iliasam/OpenSimpleLidar/Mechanics/Base_plate/base_plate.png

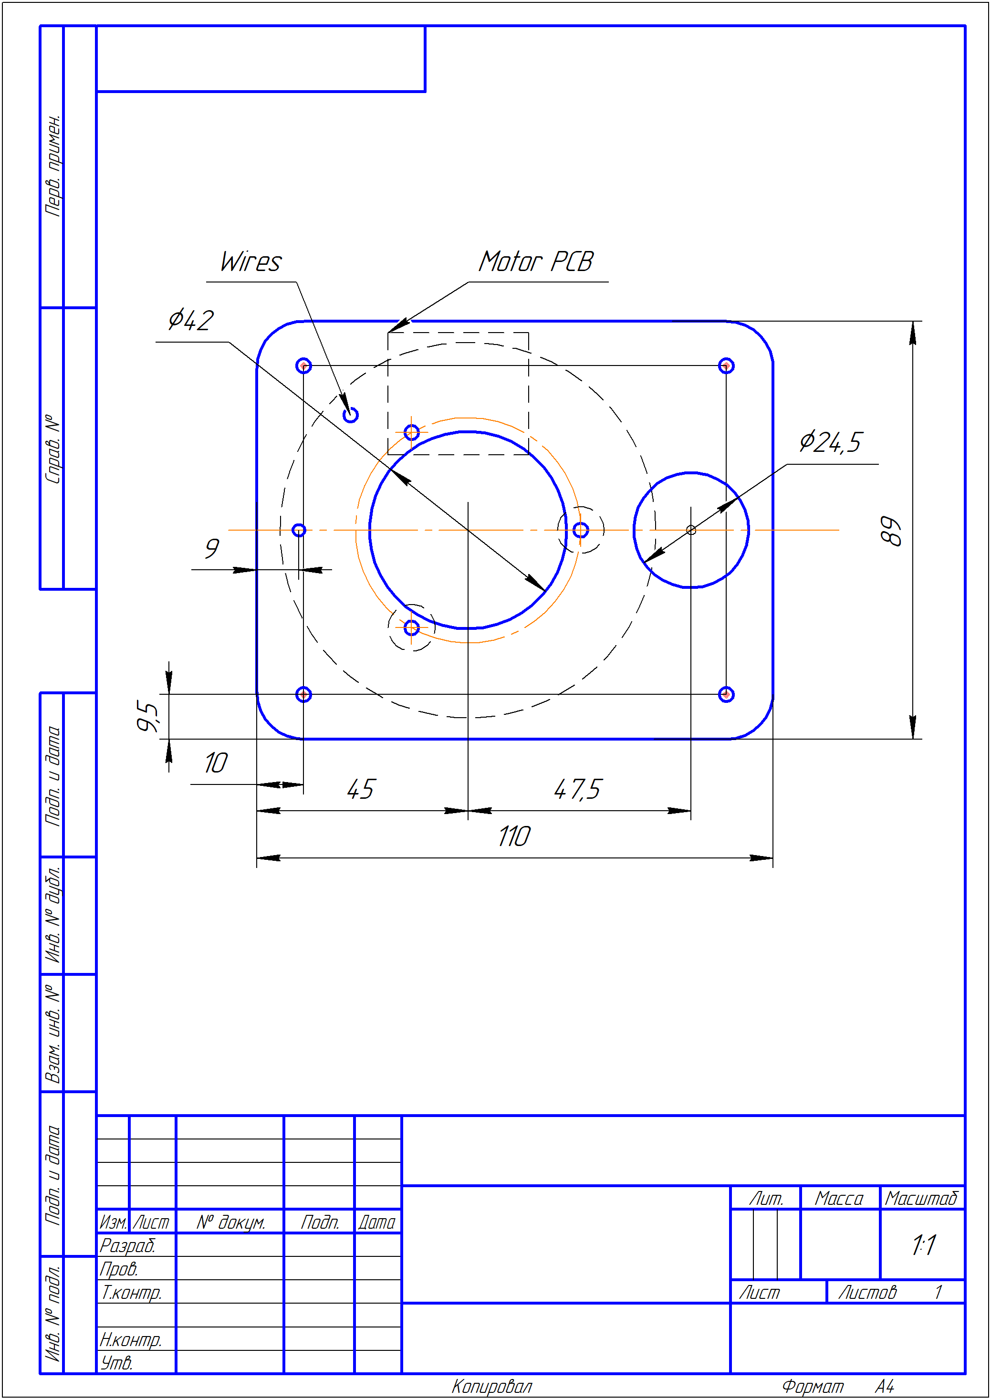
Mechanics/Base_plate/base_plate.png
