iliasam/OpenSimpleLidar/Mechanics/laser_angle.png

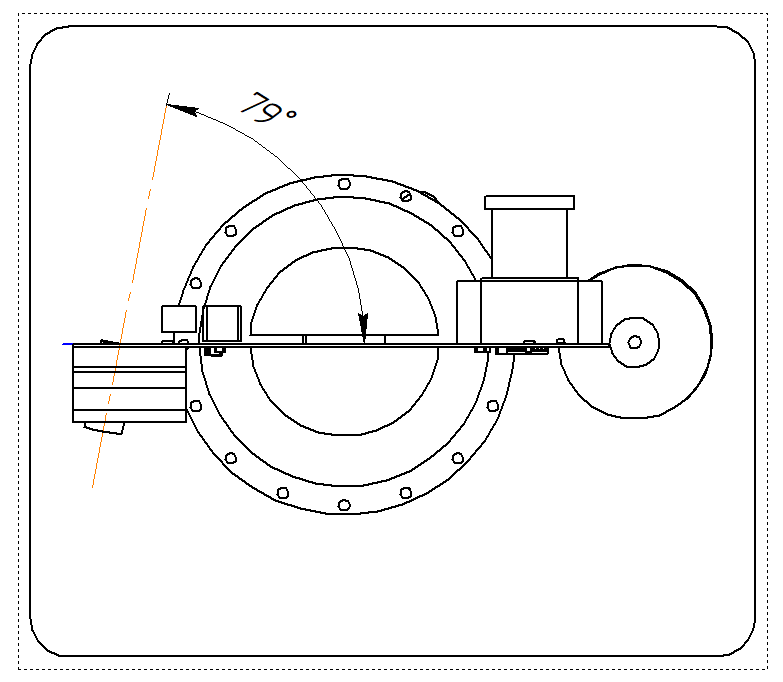
Mechanics/laser_angle.png
