iliasam/OpenSimpleLidar/Misc/filter_photo.jpg

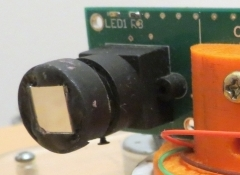
Misc/filter_photo.jpg
