iliasam/OpenSimpleLidar/Misc/finding_sensor_active_zone.png

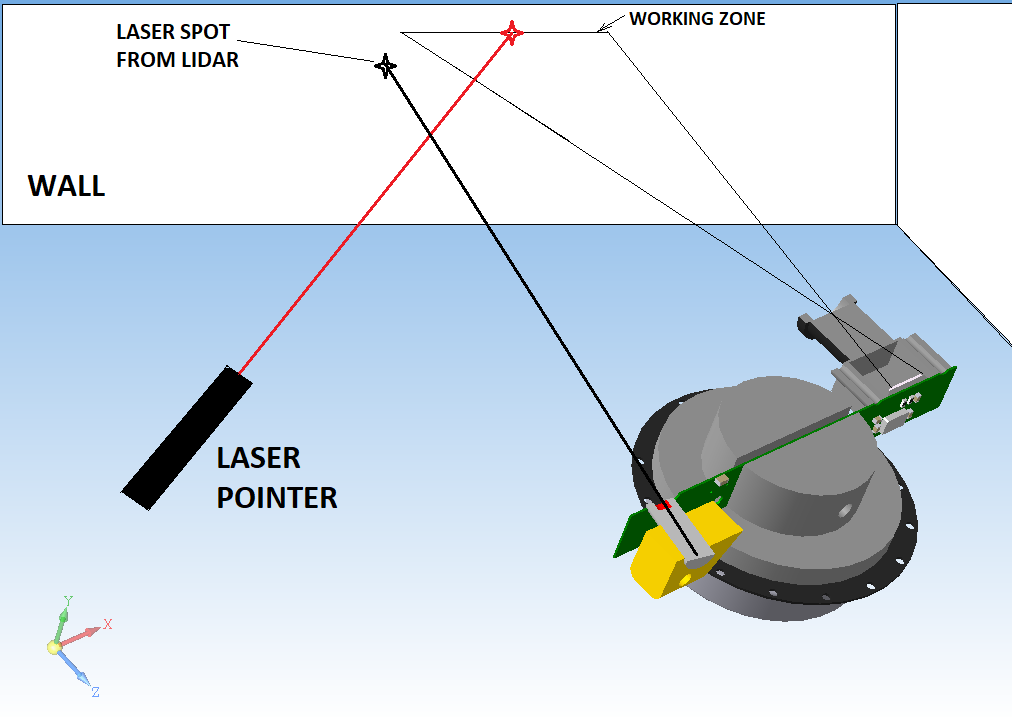
Misc/finding_sensor_active_zone.png
