iliasam/OpenSimpleLidar/Misc/interference_filter.png

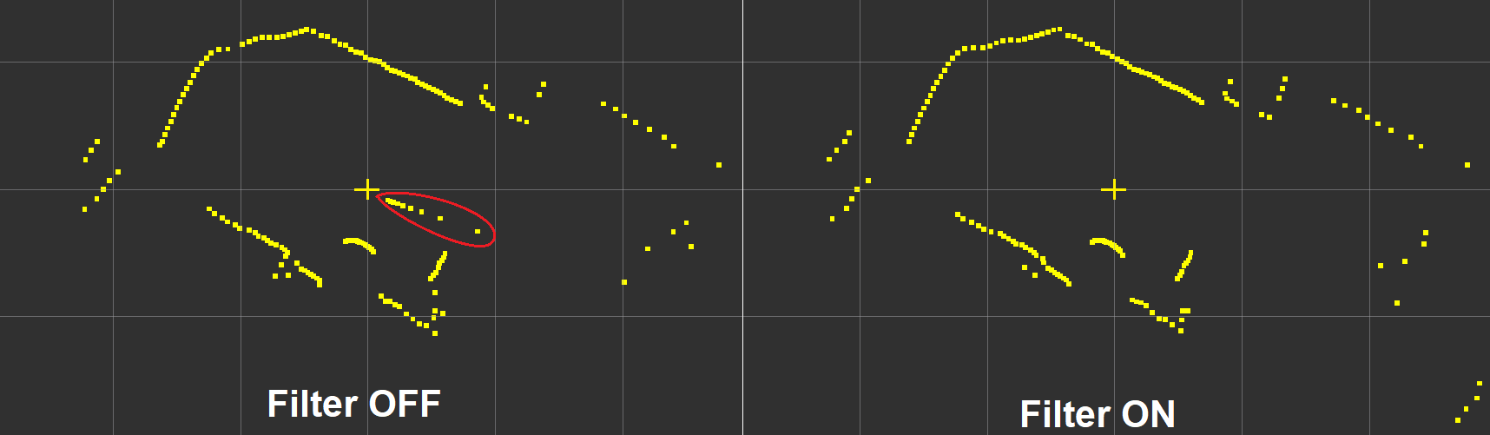
Misc/interference_filter.png
