iliasam/OpenSimpleLidar/Misc/Laser_alignment.png

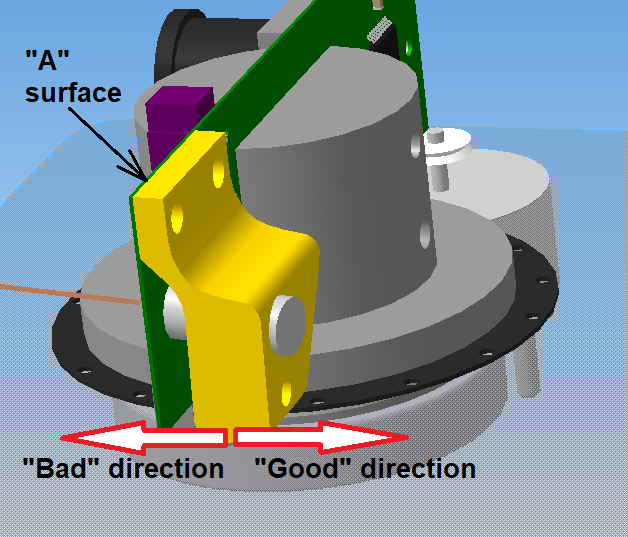
Misc/Laser_alignment.png
