iliasam/OpenSimpleLidar/Misc/Pictures/laser.jpg

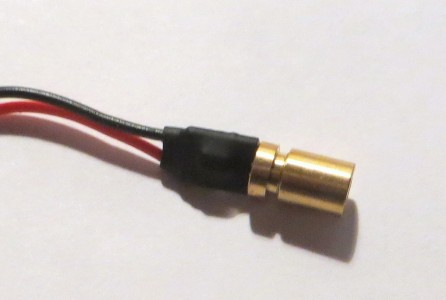
Misc/Pictures/laser.jpg
