iliasam/OpenSimpleLidar/Misc/Pictures/laser_holder.jpg

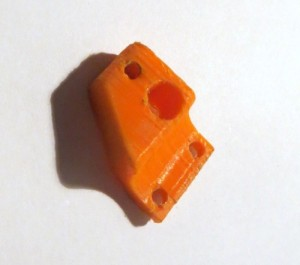
Misc/Pictures/laser_holder.jpg
