iliasam/OpenSimpleLidar/Misc/Pictures/pcb_holder1.jpg

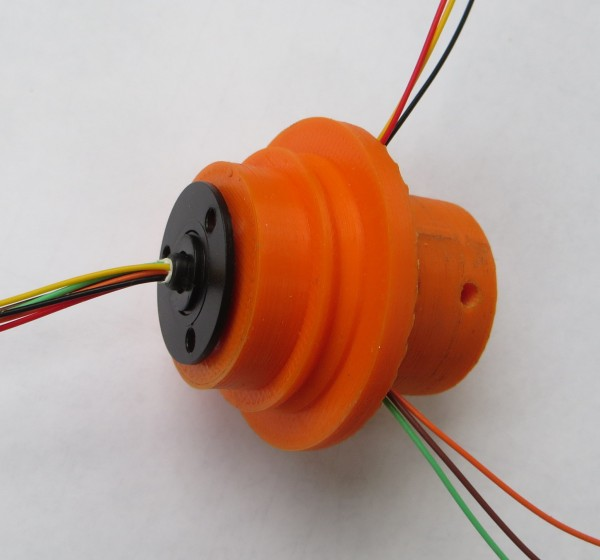
Misc/Pictures/pcb_holder1.jpg
