iliasam/OpenSimpleLidar/Misc/Pictures/pcb_holder2.JPG

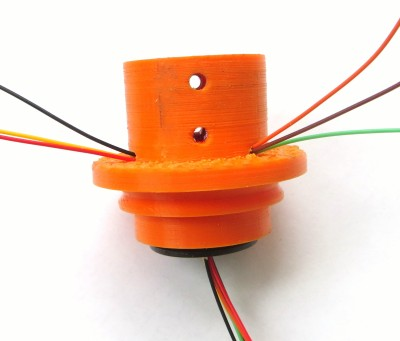
Misc/Pictures/pcb_holder2.JPG
