iliasam/OpenSimpleLidar/Misc/Pictures/pcb_holder_and_encoder.jpg

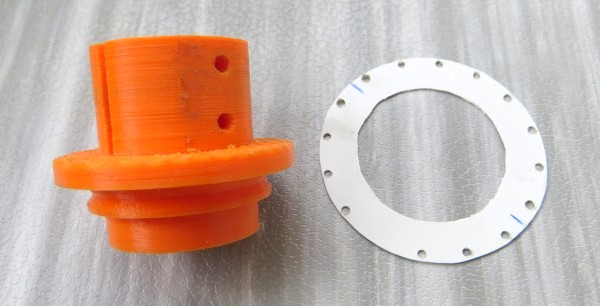
Misc/Pictures/pcb_holder_and_encoder.jpg
