iliasam/OpenSimpleLidar/Misc/Pictures/pic1.png

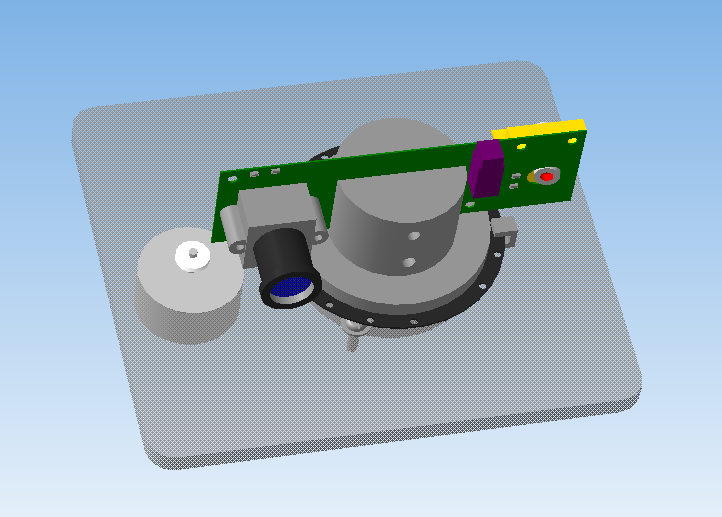
Misc/Pictures/pic1.png
