iliasam/OpenSimpleLidar/Misc/Pictures/pic2.png

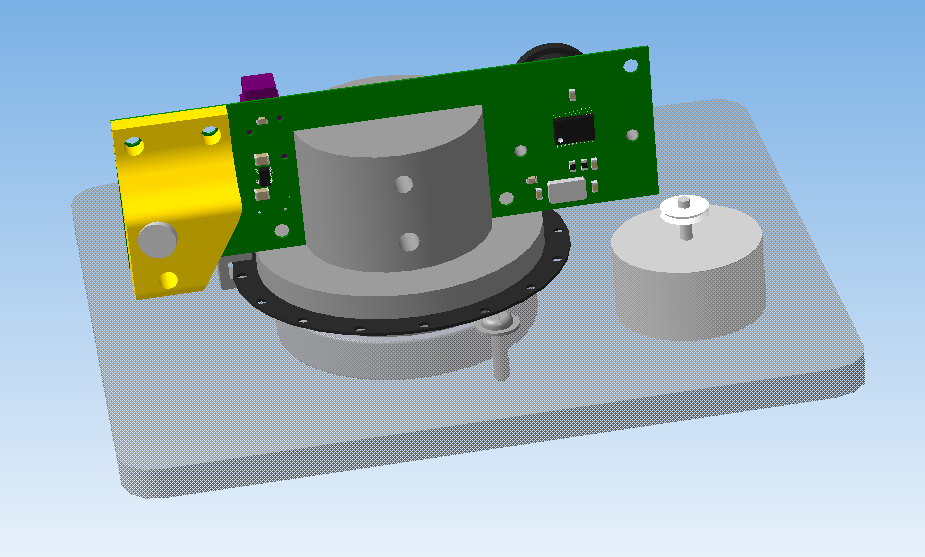
Misc/Pictures/pic2.png
