iliasam/OpenSimpleLidar/Misc/Pictures/pic3.png

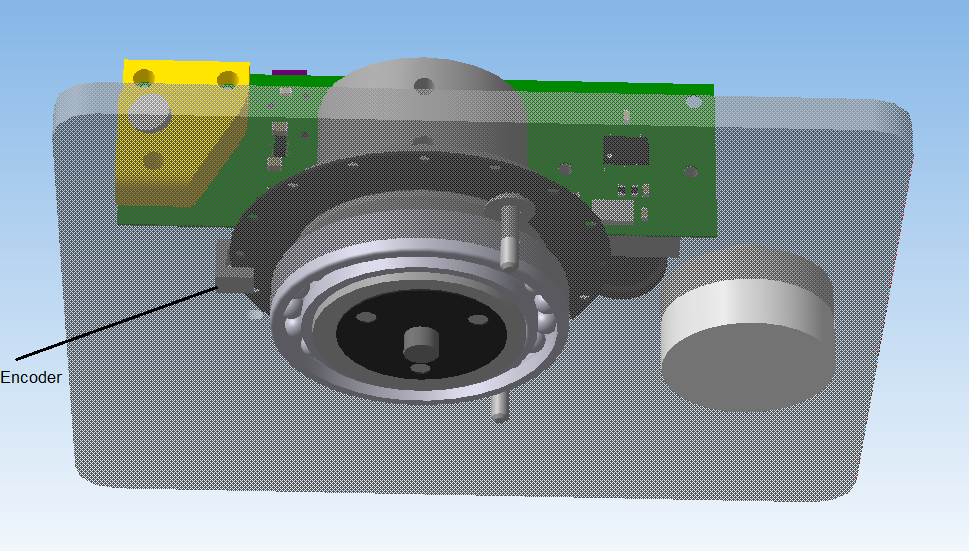
Misc/Pictures/pic3.png
