iliasam/OpenSimpleLidar/Misc/RobotStructure.png

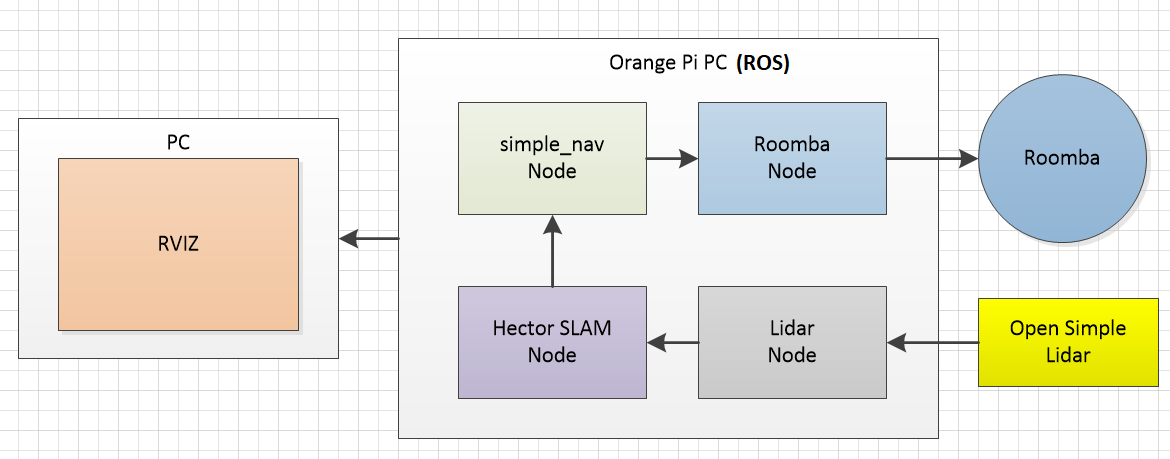
Misc/RobotStructure.png
