iliasam/OpenSimpleLidar/PCB/CommonPCB_v1.2M/PCB_top_v1.2M.png

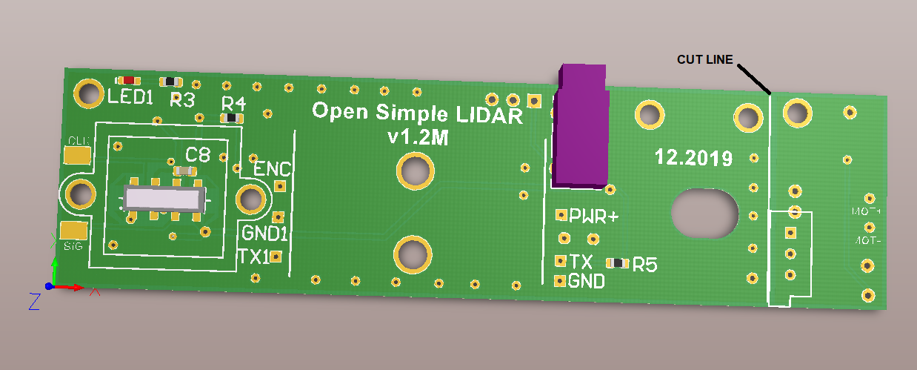
PCB/CommonPCB_v1.2M/PCB_top_v1.2M.png
