iliasam/OpenSimpleLidar/PCB/CommonPCB_v1.2M/Schematic_main_v1_2.png

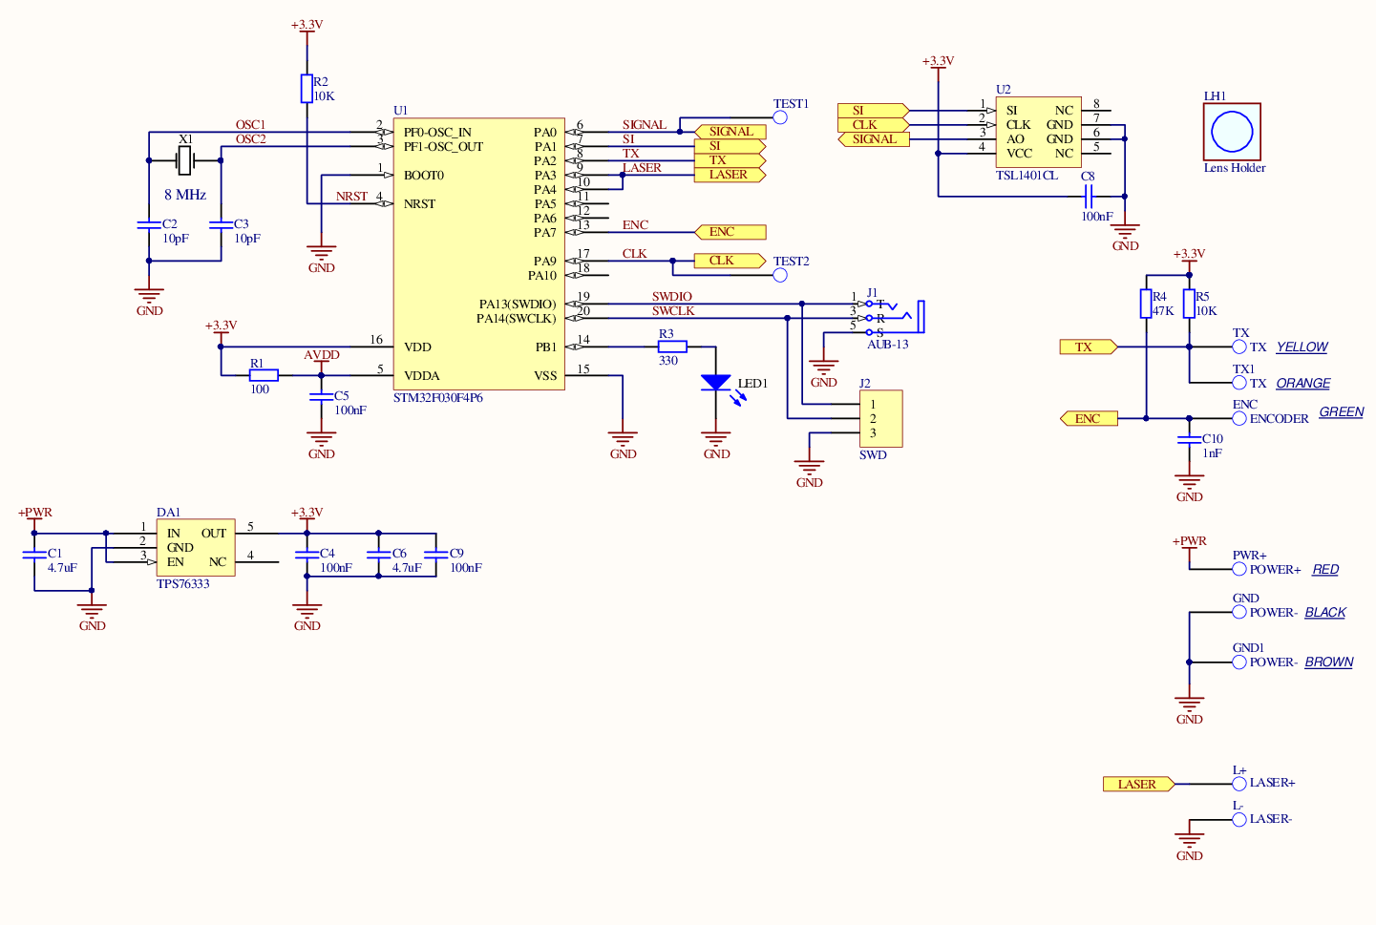
PCB/CommonPCB_v1.2M/Schematic_main_v1_2.png
