iliasam/OpenSimpleLidar/PCB/CommonPCB_v1.2M/Schematic_motor_v1.2.png

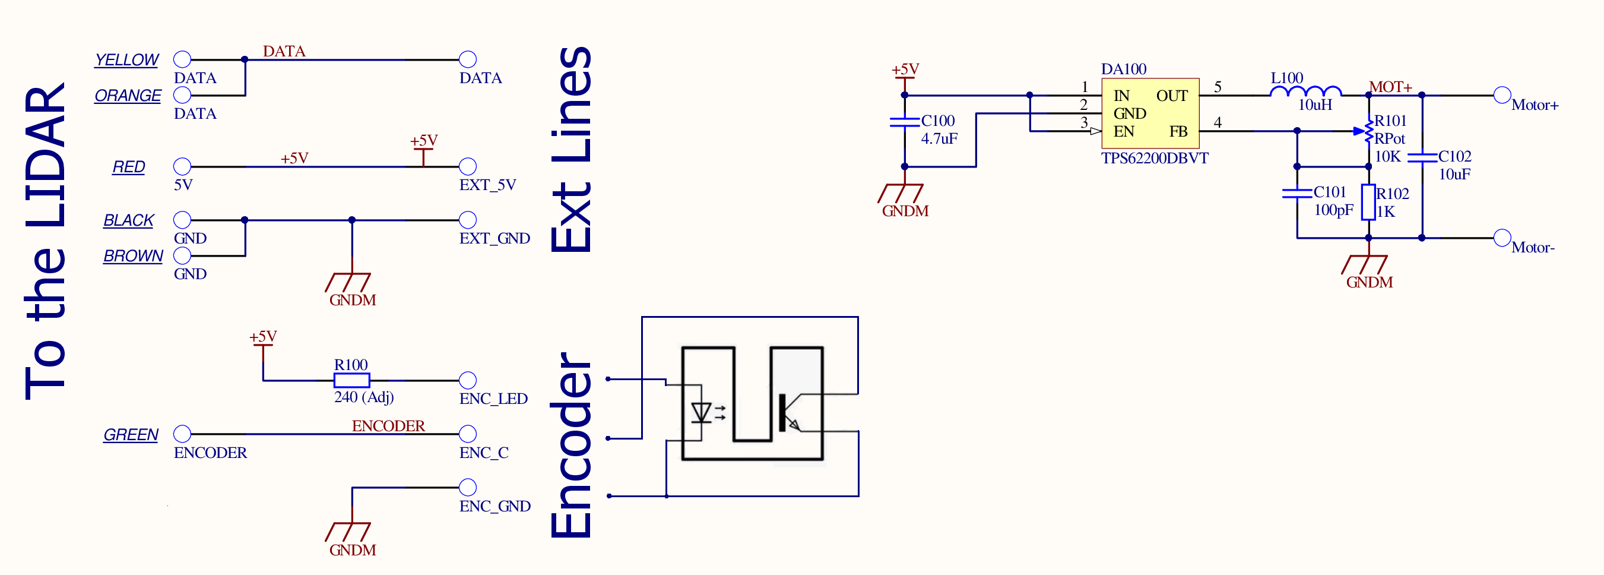
PCB/CommonPCB_v1.2M/Schematic_motor_v1.2.png
