iliasam/OpenSimpleLidar/PCB/SplittedPCB_v1.0_and_v1.1/MainPCB/PCB_assemply_top_v1.1.png

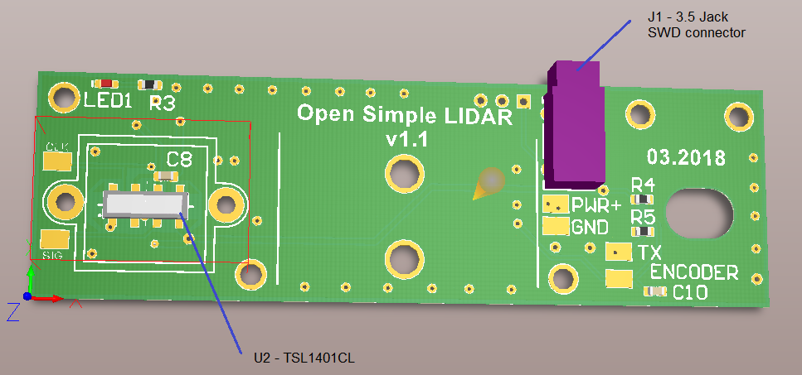
PCB/SplittedPCB_v1.0_and_v1.1/MainPCB/PCB_assemply_top_v1.1.png
