iliasam/OpenSimpleLidar/PCB/SplittedPCB_v1.0_and_v1.1/MotorPCB_v1.0/PCB_Connections.png

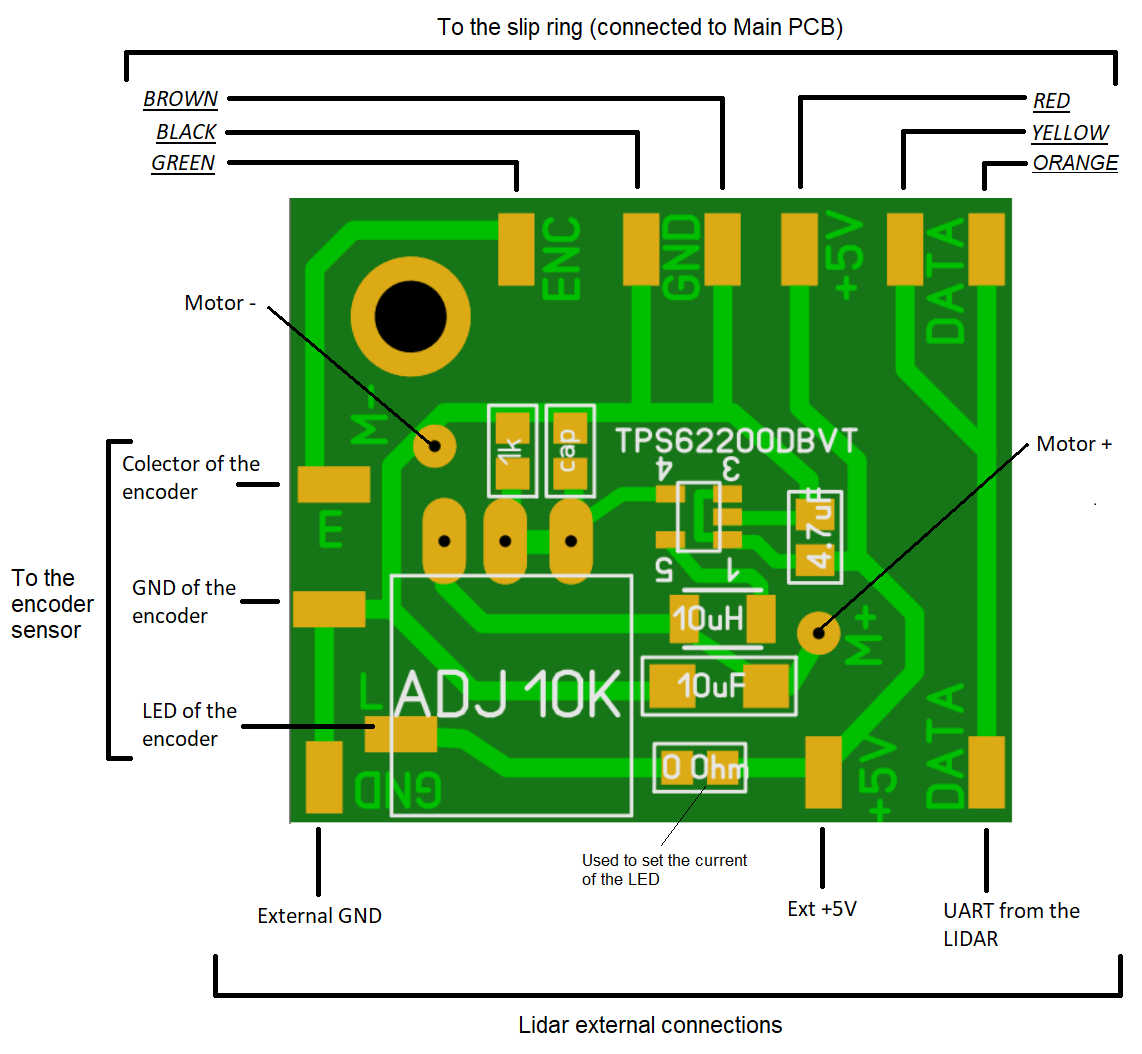
PCB/SplittedPCB_v1.0_and_v1.1/MotorPCB_v1.0/PCB_Connections.png
