iliasam/OpenSimpleLidar/Misc/Pictures/installing_sensor.jpg

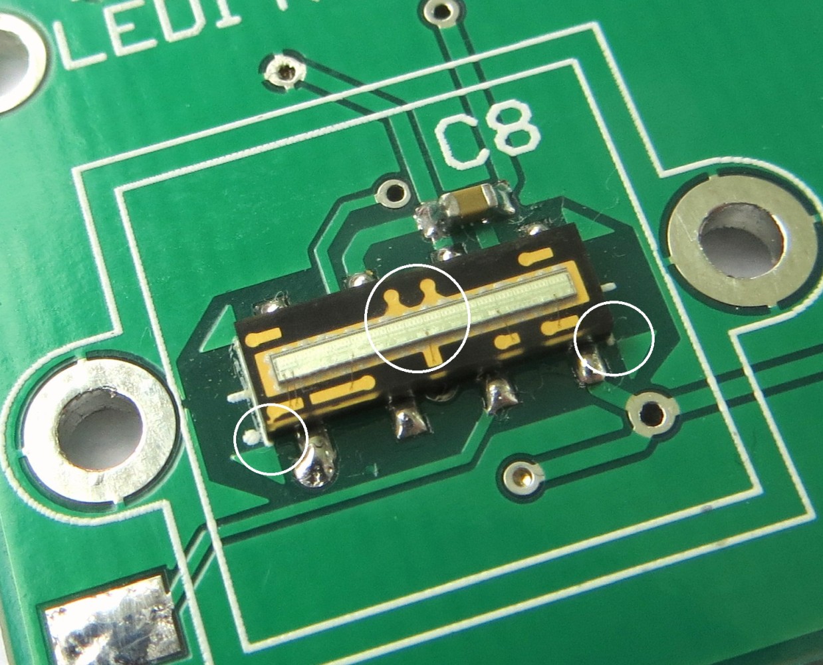
Misc/Pictures/installing_sensor.jpg
