iliasam/OpenSimpleLidar/Misc/Pictures/installing_slip_ring.jpg

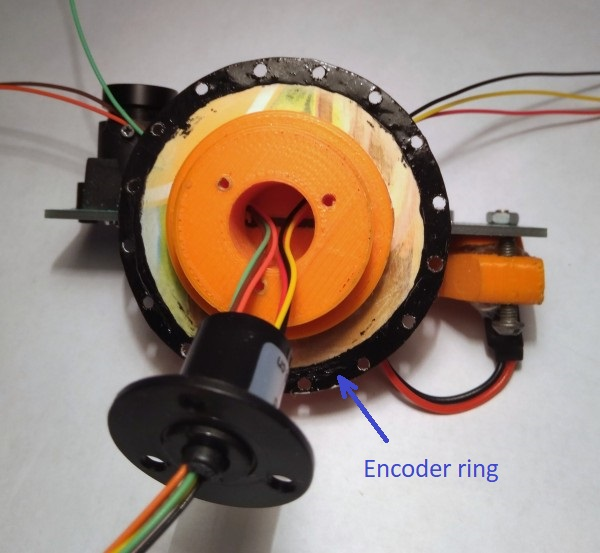
Misc/Pictures/installing_slip_ring.jpg
