iliasam/OpenSimpleLidar/Misc/Pictures/laser_holder_installed.jpg

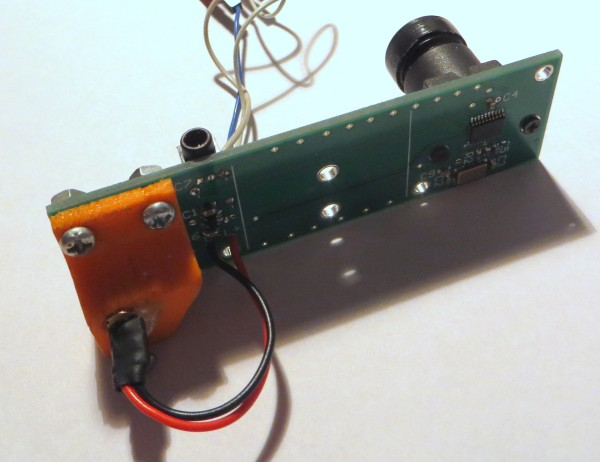
Misc/Pictures/laser_holder_installed.jpg
