iliasam/OpenSimpleLidar/Misc/Pictures/laser_installed.jpg

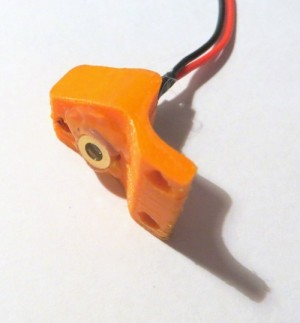
Misc/Pictures/laser_installed.jpg
