iliasam/OpenSimpleLidar/Misc/Pictures/lens_installed.jpg

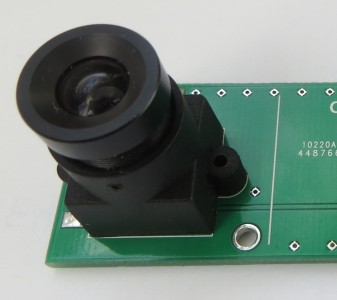
Misc/Pictures/lens_installed.jpg
