iliasam/OpenSimpleLidar/PCB/CommonPCB_v1.1M/PCB_assembly_bottom_v1.1M.png

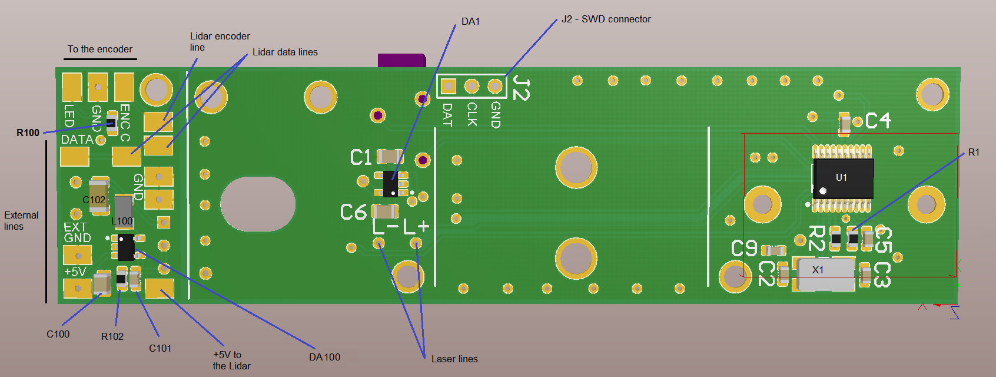
PCB/CommonPCB_v1.1M/PCB_assembly_bottom_v1.1M.png
