iliasam/OpenSimpleLidar/PCB/CommonPCB_v1.1M/PCB_assembly_top_v1.1M.png

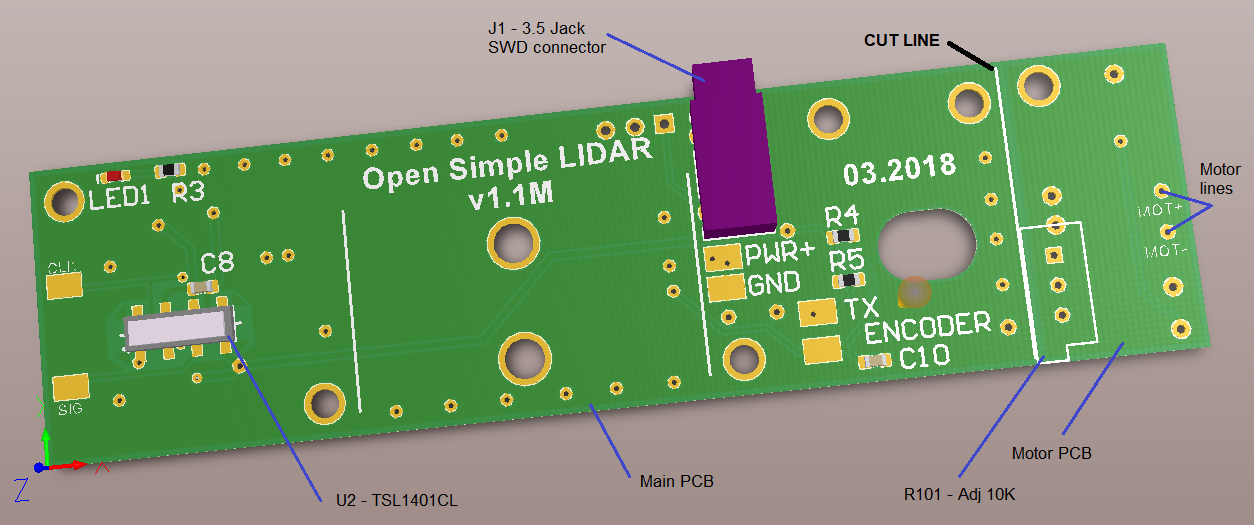
PCB/CommonPCB_v1.1M/PCB_assembly_top_v1.1M.png
