iliasam/OpenSimpleLidar/PCB/CommonPCB_v1.2/PCB_assembly_top_v1.2.png

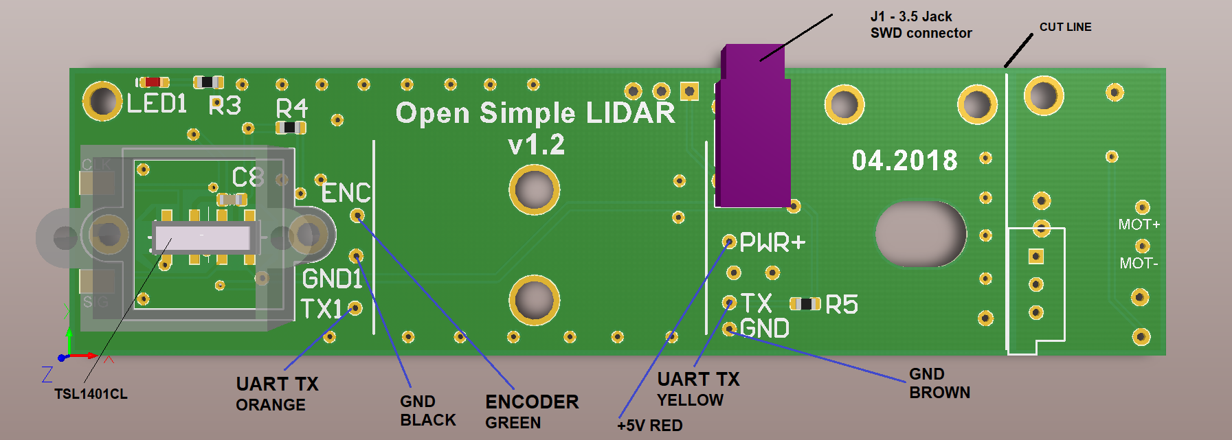
PCB/CommonPCB_v1.2/PCB_assembly_top_v1.2.png
