iliasam/OpenSimpleLidar/Misc/test_laser_on.jpg

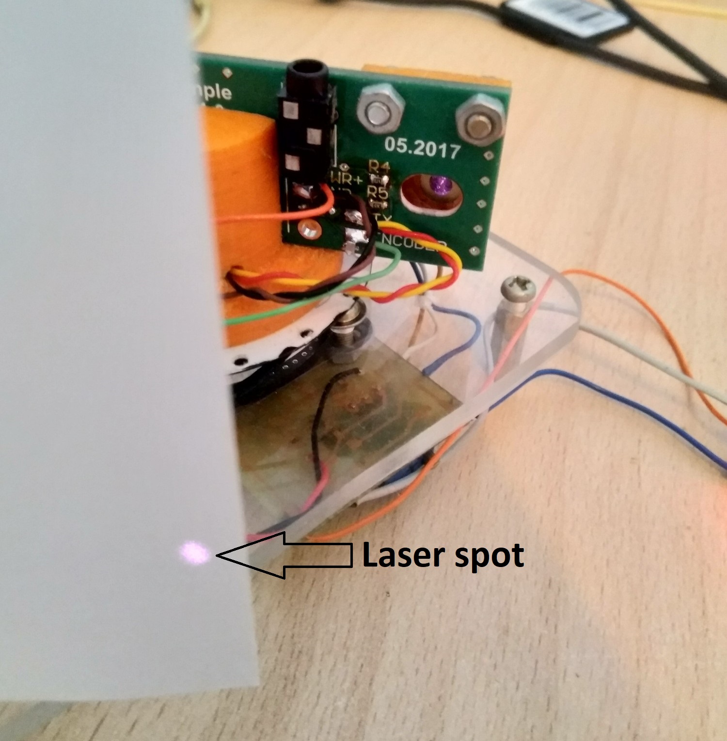
Misc/test_laser_on.jpg
