iliasam/OpenSimpleLidar/Firmware/lidar4_main_code/init_periph.h

#ifndef _INIT_PERIPH_H
#define _INIT_PERIPH_H

#include "stm32f0xx.h"

#define TIM1_PRESCALER  0

//STM32F030 ADC max sample rate is 1 MSPS
#define ADC_FREQUENCY   480000//Hz
#define TIM1_PERIOD     ((SystemCoreClock / ADC_FREQUENCY) - 1)

//Undone
//For dummy capture
//#define ADC_FREQUENCY_FAST      800000//Hz
//#define TIM1_PERIOD_FAST        ((SystemCoreClock / ADC_FREQUENCY_FAST) - 1)

typedef enum
{
  CLK_PWM = 0,
  CLK_GPIO,
}ClkPinType;

//TSL1401 SI pin
#define SI_PIN                  GPIO_Pin_1
#define SI_PORT                 GPIOA

//TSL1401 CLK pin
#define CLK_PIN                 GPIO_Pin_9 //TIM1_CH2
#define CLK_PORT                GPIOA

//Laser modulation controlling
#define LASER_PINS              (GPIO_Pin_3 | GPIO_Pin_4)
#define LASER_PORT              GPIOA

//LED output
#define LED_PIN                 GPIO_Pin_1
#define LED_PORT                GPIOB

//ADC input
#define ADC_PIN                 GPIO_Pin_0
#define ADC_PORT                GPIOA

//Encoder input
#define ENCODER_PIN             GPIO_Pin_7//tim17_ch1
#define ENCODER_PIN_SRC         GPIO_PinSource7
#define ENCODER_PORT            GPIOA

//UART line
#define UART_TX_PIN             GPIO_Pin_2
#define UART_TX_PORT            GPIOA
#define UART_TX_PINSOURCE       GPIO_PinSource2

#define UART_TX_DMA_CHANNEL     DMA1_Channel2
#define UART_TX_DMA_FLAG        DMA1_FLAG_TC2
#define UART_TX_DMA_FLAGE       DMA1_FLAG_TE2

#define ADC_DMA_CHANNEL         DMA1_Channel1


void init_all_periph(void);
void init_clk(void);

void capture_start(volatile uint16_t* pointer);
void stop_hardware_capture(void);

void enable_laser(void);
void disable_laser(void);

void switch_led(uint8_t val);
void delay_ms(uint32_t ms);

void switch_capture_speed(uint8_t is_high_speed);

#endif
